kondovskii/pocket-pet/firmware/pocket-pet-board/Core/Inc/pocket_pet_pins.h

#ifndef POCKET_PET_PINS_H
#define POCKET_PET_PINS_H

#include "main.h"

/*
 * Board pin abstraction.
 *
 * Driver code never names a GPIO port or pin directly — only the symbols
 * below. Moving the firmware between the Nucleo bench setup and the custom
 * board changes only this file.
 */

/* ---- Pin aliases -------------------------------------------------------- */
/* These alias the CubeMX-generated labels from main.h, so the .ioc stays the
 * single source of truth. */

#define OLED_CS_PORT     OLED_CS_GPIO_Port
#define OLED_CS_PIN      OLED_CS_Pin

#define OLED_DC_PORT     OLED_DC_GPIO_Port
#define OLED_DC_PIN      OLED_DC_Pin

#define OLED_RST_PORT    OLED_RST_GPIO_Port
#define OLED_RST_PIN     OLED_RST_Pin

#define OLED_SPI         hspi1

/* ---- Board selection ---------------------------------------------------- */
/* Exactly one. This is the only line that differs between targets. */
/* #define BOARD_NUCLEO */
#define BOARD_POCKET_PET_V1

#if defined(BOARD_POCKET_PET_V1)
  /* J6 ties SA0 to GND and CS to 3V3, so the address is 0x18. */
  #define LIS3DH_ADDR_7BIT   0x18
#elif defined(BOARD_NUCLEO)
  /* SA0 and CS float on the bench wiring; the module's own strapping
   * gives 0x19. */
  #define LIS3DH_ADDR_7BIT   0x19
#else
  #error "No board selected in pocket_pet_pins.h"
#endif

#endif /* POCKET_PET_PINS_H */
